addrummond/mlm/firmware/capsense.c

#include <capsense.h>
#include <config.h>
#include <const.h>
#include <em_acmp.h>
#include <em_cmu.h>
#include <em_emu.h>
#include <em_gpio.h>
#include <em_lesense.h>
#include <em_wdog.h>
#include <em_pcnt.h>
#include <em_prs.h>
#include <em_rtc.h>
#include <leds.h>
#include <myemu.h>
#include <rtc.h>
#include <rtt.h>
#include <stdbool.h>
#include <time.h>

// https://www.silabs.com/content/usergenerated/asi/cloud/attachments/siliconlabs/en/community/mcu/32-bit/knowledge-base/jcr:content/content/primary/blog/low_power_capa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

static uint32_t touch_chan;
static uint32_t touch_acmp;

static volatile uint32_t old_count;

uint32_t calibration_values[3] __attribute__((section (".persistent")));
uint32_t le_calibration_center_pad_value __attribute__((section (".persistent")));
uint32_t le_calibration_center_pad_threshold __attribute__((section (".persistent")));

static const uint32_t THRESHOLD_FRAC = 218;
// The left and right buttons are often pressed with the edge of the thumb, so a little more sensitivity is needed.
static const uint32_t LEFT_RIGHT_THRESHOLD_FRAC = 223;

static const PCNT_Init_TypeDef initPCNT =
{
    .mode        = pcntModeExtSingle, // External, single mode.
    .counter     = 0,                 // Counter value has been initialized to 0.
    .top         = 0xFFFF,            // Counter top value.
    .negEdge     = false,             // Use positive edge.
    .countDown   = false,             // Up-counting.
    .filter      = false,             // Filter disabled.
    .hyst        = false,             // Hysteresis disabled.
    .s1CntDir    = false,             // Counter direction is given by S1.
    .cntEvent    = pcntCntEventUp,    // Regular counter counts up on upcount events.
    .auxCntEvent = pcntCntEventNone,  // Auxiliary counter doesn't respond to events.
    .s0PRS       = pcntPRSCh0,        // PRS channel 0 selected as S0IN.
    .s1PRS       = pcntPRSCh1         // PRS channel 1 selected as S1IN.
};

void setup_capsense()
{
    ACMP_CapsenseInit_TypeDef capsenseInit = ACMP_CAPSENSE_INIT_DEFAULT;
    CMU_ClockEnable(cmuClock_ACMP0, true);
    CMU_ClockEnable(cmuClock_ACMP1, true);
    CMU_ClockEnable(cmuClock_PRS, true);
    CMU_ClockEnable(cmuClock_PCNT0, true);
    ACMP_CapsenseInit(ACMP0, &capsenseInit);
    ACMP_CapsenseInit(ACMP1, &capsenseInit);

    while (!(ACMP0->STATUS & ACMP_STATUS_ACMPACT) || !(ACMP1->STATUS & ACMP_STATUS_ACMPACT))
        ;

    PRS_SourceAsyncSignalSet(0, PRS_CH_CTRL_SOURCESEL_ACMP0, PRS_CH_CTRL_SIGSEL_ACMP0OUT);

    PCNT_Init(PCNT0, &initPCNT);

    PCNT_PRSInputEnable(PCNT0, pcntPRSInputS0, true);

    // Sync up to end PCNT initialization
    while (PCNT0->SYNCBUSY)
    {
        PRS_LevelSet(PRS_SWLEVEL_CH0LEVEL, PRS_SWLEVEL_CH0LEVEL);
        PRS_LevelSet(~PRS_SWLEVEL_CH0LEVEL, PRS_SWLEVEL_CH0LEVEL);
    }

    ACMP_CapsenseChannelSet(ACMP0, acmpChannel1);

    touch_acmp = 0;
    touch_chan = 0;
    old_count = 0;
}

void disable_capsense()
{
    PCNT_PRSInputEnable(PCNT0, pcntPRSInputS0, false);
    PCNT_Enable(PCNT0, pcntModeDisable);
    ACMP0->CTRL &= ~ACMP_CTRL_IRISE_ENABLED;
    ACMP1->CTRL &= ~ACMP_CTRL_IRISE_ENABLED;
    ACMP_Disable(ACMP0);
    ACMP_Disable(ACMP1);
    NVIC_ClearPendingIRQ(ACMP0_IRQn);
    NVIC_DisableIRQ(ACMP0_IRQn);
    CMU_ClockEnable(cmuClock_ACMP0, false);
    CMU_ClockEnable(cmuClock_ACMP1, false);
    CMU_ClockEnable(cmuClock_PRS, false);
    CMU_ClockEnable(cmuClock_PCNT0, false);
}

void cycle_capsense()
{
    PCNT_PRSInputEnable(PCNT0, pcntPRSInputS0, false);

    if (touch_acmp == 0) {
        if (touch_chan == 0) {
            ACMP_CapsenseChannelSet(ACMP0, acmpChannel1);
            touch_chan = 1;
        } else {
            ACMP0->CTRL &= ~ACMP_CTRL_IRISE_ENABLED;
            ACMP1->CTRL |= ACMP_CTRL_IRISE_ENABLED;
            ACMP_CapsenseChannelSet(ACMP1, acmpChannel6);
            PRS_SourceAsyncSignalSet(0, PRS_CH_CTRL_SOURCESEL_ACMP1, PRS_CH_CTRL_SIGSEL_ACMP1OUT);
            touch_acmp = 1;
            touch_chan = 0;
        }
    } else {
        ACMP1->CTRL &= ~ACMP_CTRL_IRISE_ENABLED;
        ACMP0->CTRL |= ACMP_CTRL_IRISE_ENABLED;
        ACMP_CapsenseChannelSet(ACMP0, acmpChannel0);
        PRS_SourceAsyncSignalSet(0, PRS_CH_CTRL_SOURCESEL_ACMP0, PRS_CH_CTRL_SIGSEL_ACMP0OUT);

        touch_acmp = 0;
        touch_chan = 0;
    }

    PCNT_PRSInputEnable(PCNT0, pcntPRSInputS0, true);

    // Sync up to end PCNT initialization
    while (PCNT0->SYNCBUSY)
    {
        PRS_LevelSet(PRS_SWLEVEL_CH0LEVEL, PRS_SWLEVEL_CH0LEVEL);
        PRS_LevelSet(~PRS_SWLEVEL_CH0LEVEL, PRS_SWLEVEL_CH0LEVEL);
    }

    old_count = PCNT0->CNT;
}

void calibrate_capsense()
{
    setup_capsense();

    delay_ms_cyc_prepare {
        get_touch_count(0, 0, 0); // clear any nonsense values
    }
    uint32_t ellapsed = delay_ms_cyc(PAD_COUNT_MS);

    uint32_t count, chan;
    uint32_t chans_done = 0;
    do {
        get_touch_count(&count, &chan, ellapsed);
        if (! (chans_done & (1 << chan))) {
            calibration_values[chan] = count;
            chans_done |= (1 << chan);
        }
        
        cycle_capsense();
        delay_ms_cyc_prepare {
            get_touch_count(0, 0, 0); // clear any nonsense value
        }

        ellapsed = delay_ms_cyc(PAD_COUNT_MS);
    } while (chans_done != 0b111);

    disable_capsense();

    SEGGER_RTT_printf(0, "Touch calibration: %u %u %u\n", calibration_values[0], calibration_values[1], calibration_values[2]);
}

void calibrate_le_capsense()
{
    setup_le_capsense_oneshot();
    my_emu_enter_em2(true);
    le_calibration_center_pad_value = lesense_result;
    le_calibration_center_pad_threshold = le_calibration_center_pad_value * THRESHOLD_FRAC / 256;
    disable_le_capsense();

    SEGGER_RTT_printf(0, "LE touch calibration: %u\n", le_calibration_center_pad_value);
}

static uint32_t rat0nopress, rat1nopress, rat2nopress, rat3nopress, rat4nopress;

touch_position get_touch_position(uint32_t chan0, uint32_t chan1, uint32_t chan2)
{
    // Generous margin here because temperature changes can have quite a large effect.
    if (chan0 > calibration_values[0] * 3 || chan1 > calibration_values[1] * 3 || chan2 > calibration_values[2] * 3)
        return NO_TOUCH_DETECTED;

    if (rat0nopress == 0) {
        rat0nopress = (calibration_values[0] << 8) / calibration_values[2];
        rat1nopress = (calibration_values[1] << 8) / calibration_values[2];
        rat2nopress = (calibration_values[2] << 8) / (calibration_values[0] + calibration_values[1]);

        rat3nopress = (calibration_values[0] << 8) / calibration_values[1];
        rat4nopress = (calibration_values[1] << 8) / calibration_values[0];
    }

    uint32_t rat0 = (chan0 << 8) / chan2;
    uint32_t rat1 = (chan1 << 8) / chan2;
    uint32_t rat2 = (chan2 << 8) / (chan0 + chan1);
    uint32_t rat3 = (chan0 << 8) / chan1;
    uint32_t rat4 = (chan1 << 8) / chan0;

    if (rat0 < THRESHOLD_FRAC * rat0nopress / 256 && rat1 < rat1nopress * THRESHOLD_FRAC / 256)
        return LEFT_AND_RIGHT_BUTTONS;
    if (rat2 < THRESHOLD_FRAC * rat2nopress / 256)
        return CENTER_BUTTON;
    if (rat0 < LEFT_RIGHT_THRESHOLD_FRAC * rat0nopress / 256 && rat3 < THRESHOLD_FRAC * rat3nopress / 256)
        return RIGHT_BUTTON;
    if (rat1 < LEFT_RIGHT_THRESHOLD_FRAC * rat1nopress / 256 && rat4 < THRESHOLD_FRAC * rat4nopress / 256)
        return LEFT_BUTTON;

    return NO_TOUCH_DETECTED;
}

bool le_center_pad_is_touched(uint32_t chan2)
{
    return chan2 != 0 && chan2 < le_calibration_center_pad_threshold;
}

uint32_t get_touch_count_func(uint32_t *chan_value, uint32_t *chan, uint32_t millisecond_sixteenths, const char *src_pos)
{
    if (chan != 0)
        *chan = (touch_acmp << 1) | touch_chan;

    uint32_t raw_count = PCNT0->CNT;

    if (millisecond_sixteenths > PAD_COUNT_MS*16*2) {
        if (chan_value != 0)
            *chan_value = ((1 << 30)-1) | (1 << 30);
        old_count = PCNT0->CNT;
        return raw_count;
    }

    uint32_t uncompensated_count;
    if (chan_value != 0) {
        if (raw_count >= old_count)
            uncompensated_count = raw_count - old_count;
        else
            uncompensated_count = ((1 << PCNT0_CNT_SIZE) + raw_count) - old_count;

        // Note that millisecond_sixteenths should always be >= (PAD_COUNT_MS * 16)
        uint32_t compensated_count = (uncompensated_count * (PAD_COUNT_MS * 16)) / millisecond_sixteenths;
        *chan_value = compensated_count;
    }

    old_count = PCNT0->CNT;

    return raw_count;
}

static const uint16_t LESENSE_ACMP_VDD_SCALE = 0x37U;

#define LESENSE_CAPSENSE_CH_CONF_SLEEP                                                                   \
  {                                                                                                      \
    true,                     /* Enable scan channel. */                                                 \
    true,                     /* Enable the assigned pin on scan channel. */                             \
    true,                     /* Enable interrupts on channel. */                                        \
    lesenseChPinExDis,        /* GPIO pin is disabled during the excitation period. */                   \
    lesenseChPinIdleDis,      /* GPIO pin is disabled during the idle period. */                         \
    false,                    /* Don't use alternate excitation pins for excitation. */                  \
    false,                    /* Disabled to shift results from this channel to the decoder register. */ \
    false,                    /* Disabled to invert the scan result bit. */                              \
    true,                     /* Enabled to store counter value in the result buffer. */                 \
    lesenseClkLF,             /* Use the LF clock for excitation timing. */                              \
    lesenseClkLF,             /* Use the LF clock for sample timing. */                                  \
    0,                        /* Excitation time is set to 0 excitation clock cycles. */                 \
    LE_PAD_CLOCK_COUNT,       /* Sample delay */                                                         \
    0,                        /* Measure delay */                                                        \
    LESENSE_ACMP_VDD_SCALE,   /* ACMP threshold has been set to LESENSE_ACMP_VDD_SCALE. */               \
    lesenseSampleModeCounter, /* Counter will be used in comparison. */                                  \
    lesenseSetIntLevel,       /* Interrupt is generated if the sensor triggers. */                       \
    0x00,                     /* Counter threshold has been set to 0x0. */                               \
    lesenseCompModeLess       /* Compare mode has been set to trigger interrupt on >= */                 \
  }

#define LESENSE_CAPSENSE_CH_CONF_SENSE                                                                   \
  {                                                                                                      \
    true,                     /* Enable scan channel. */                                                 \
    true,                     /* Enable the assigned pin on scan channel. */                             \
    false,                    /* Disable interrupts on channel. */                                       \
    lesenseChPinExDis,        /* GPIO pin is disabled during the excitation period. */                   \
    lesenseChPinIdleDis,      /* GPIO pin is disabled during the idle period. */                         \
    false,                    /* Don't use alternate excitation pins for excitation. */                  \
    false,                    /* Disabled to shift results from this channel to the decoder register. */ \
    false,                    /* Disabled to invert the scan result bit. */                              \
    true,                     /* Enabled to store counter value in the result buffer. */                 \
    lesenseClkLF,             /* Use the LF clock for excitation timing. */                              \
    lesenseClkLF,             /* Use the LF clock for sample timing. */                                  \
    0,                        /* Excitation time is set to ___ excitation clock cycles. */               \
    LE_PAD_CLOCK_COUNT,       /* Sample delay is set to ___ sample clock cycles. */                      \
    0,                        /* Measure delay is set to ___ excitation clock cycles.*/                  \
    LESENSE_ACMP_VDD_SCALE,   /* ACMP threshold has been set to LESENSE_ACMP_VDD_SCALE. */               \
    lesenseSampleModeCounter, /* ACMP will be used in comparison. */                                     \
    lesenseSetIntLevel,       /* Interrupt is generated if the sensor triggers. */                       \
    0x0,                      /* Counter threshold has been set to 0x00. */                              \
    lesenseCompModeLess       /* Compare mode has been set to trigger interrupt on "less". */            \
  }

static CONST_IN_RAM LESENSE_ChDesc_TypeDef chanConfigSense = LESENSE_CAPSENSE_CH_CONF_SENSE;
static CONST_IN_RAM LESENSE_ChDesc_TypeDef chanConfigSleep = LESENSE_CAPSENSE_CH_CONF_SLEEP;

static CONST_IN_RAM LESENSE_Init_TypeDef initLESENSE =
{
    .coreCtrl = {
        .scanStart    = lesenseScanStartPeriodic,
        .prsSel       = lesensePRSCh0,
        .scanConfSel  = lesenseScanConfDirMap,
        .invACMP0     = false,
        .invACMP1     = false,
        .dualSample   = false,
        .storeScanRes = false,
        .bufOverWr    = true,
        .bufTrigLevel = lesenseBufTrigHalf,
        .wakeupOnDMA  = lesenseDMAWakeUpDisable,
        .biasMode     = lesenseBiasModeDutyCycle,
        .debugRun     = false
    },

    .timeCtrl = {
        .startDelay = 0U
    },

    .perCtrl = {
        .dacCh0Data     = lesenseDACIfData,
        .dacCh0ConvMode = lesenseDACConvModeDisable,
        .dacCh0OutMode  = lesenseDACOutModeDisable,
        .dacCh1Data     = lesenseDACIfData,
        .dacCh1ConvMode = lesenseDACConvModeDisable,
        .dacCh1OutMode  = lesenseDACOutModeDisable,
        .dacPresc       = 0U,
        .dacRef         = lesenseDACRefBandGap,
        .acmp0Mode      = lesenseACMPModeDisable,
        .acmp1Mode      = lesenseACMPModeMuxThres,
        .warmupMode     = lesenseWarmupModeNormal
    },

    .decCtrl = {
        .decInput  = lesenseDecInputSensorSt,
        .chkState  = false,
        .intMap    = true,
        .hystPRS0  = false,
        .hystPRS1  = false,
        .hystPRS2  = false,
        .hystIRQ   = false,
        .prsCount  = true,
        .prsChSel0 = lesensePRSCh0,
        .prsChSel1 = lesensePRSCh1,
        .prsChSel2 = lesensePRSCh2,
        .prsChSel3 = lesensePRSCh3
    }
};

static le_capsense_mode le_mode;

static uint32_t le_center_pad_count_to_threshold(uint32_t count)
{
    return count * THRESHOLD_FRAC / 256;
}

static void setup_le_capsense_helper(const LESENSE_ChDesc_TypeDef *chan_config, const LESENSE_ScanMode_TypeDef scan_mode, uint32_t scan_freq)
{
    CMU_ClockEnable(cmuClock_ACMP1, true);
    CMU_ClockEnable(cmuClock_LESENSE, true);

    CMU_ClockDivSet(cmuClock_LESENSE, cmuClkDiv_16);

    GPIO_DriveModeSet(gpioPortC, gpioDriveModeStandard);

    static CONST_IN_RAM ACMP_CapsenseInit_TypeDef initACMP = {
        .fullBias                 = true,
        .halfBias                 = true,
        .biasProg                 = 0x7,
        .warmTime                 = acmpWarmTime512,
        .hysteresisLevel          = acmpHysteresisLevel5,
        .resistor                 = acmpResistor0,
        .lowPowerReferenceEnabled = false,
        .vddLevel                 = 0x30,
        .enable                   = false
    };

    ACMP_GPIOSetup(ACMP1, 0, false, false);

    ACMP_CapsenseInit(ACMP1, &initACMP);

    LESENSE_Init(&initLESENSE, true);

    LESENSE_ScanStop();
    while (LESENSE_STATUS_SCANACTIVE & LESENSE_StatusGet())
        ;
    LESENSE_ResultBufferClear();
    LESENSE_ScanFreqSet(0, scan_freq);
    LESENSE_ClkDivSet(lesenseClkLF, lesenseClkDiv_1);

    LESENSE_ChannelConfig(chan_config, 14);

    NVIC_EnableIRQ(LESENSE_IRQn);

    LESENSE_ScanModeSet(scan_mode, true);
}

void setup_le_capsense_oneshot()
{
    le_mode = LE_CAPSENSE_SENSE;
    setup_le_capsense_helper(&chanConfigSense, lesenseScanStartOneShot, 0);
    LESENSE_IntEnable(LESENSE_IEN_SCANCOMPLETE);
}

void setup_le_capsense_sleep()
{
    le_mode = LE_CAPSENSE_SLEEP;

    setup_le_capsense_helper(&chanConfigSleep, lesenseScanStartPeriodic, NORMAL_PAD_SCAN_HZ);

    LESENSE_IntDisable(LESENSE_IEN_SCANCOMPLETE);

    while (!(LESENSE->STATUS & LESENSE_STATUS_BUFHALFFULL))
        ;
    LESENSE_ChannelThresSet(14, LESENSE_ACMP_VDD_SCALE, le_center_pad_count_to_threshold(le_calibration_center_pad_value));

    // Periodically wake up to recalibrate.
    SEGGER_RTT_printf(0, "Set recal. wakeup timer.\n");
    static CONST_IN_RAM RTC_Init_TypeDef rtc_init = {
        .enable   = true,
        .debugRun = false,
        .comp0Top = true
    };
    RTC_Init(&rtc_init);
    RTC_IntEnable(RTC_IEN_COMP0);
    NVIC_EnableIRQ(RTC_IRQn);
    set_rtc_clock_div(cmuClkDiv_32768);
    RTC_CompareSet(0, RTC->CNT + LE_CAPSENSE_CALIBRATION_INTERVAL_SECONDS);
    RTC_IntClear(RTC_IFC_COMP0);
}

void le_capsense_slow_scan()
{
    LESENSE_ScanFreqSet(0, SLOW_PAD_SCAN_HZ);
}

uint32_t lesense_result;

static volatile bool irq_handler_triggered;

void reset_lesense_irq_handler_state()
{
    irq_handler_triggered = false;
}

bool check_lesense_irq_handler()
{
    bool v = irq_handler_triggered;
    irq_handler_triggered = false;
    return v;
}

void LESENSE_IRQHandler(void)
{
    irq_handler_triggered = true;

    LESENSE_IntClear(LESENSE_IEN_SCANCOMPLETE);
    LESENSE_IntClear(LESENSE_IF_CH14);

    lesense_result = LESENSE_ScanResultDataGet();

    // Stop additional interrupts screwing things up by setting threshold to zero.
    if (le_mode == LE_CAPSENSE_SLEEP)
        LESENSE_ChannelThresSet(14, LESENSE_ACMP_VDD_SCALE, 0);
}

static uint32_t get_max_value(volatile uint32_t* A, int N){
    int i;
    uint32_t max = 0;

    for (i = 0; i < N; i++) {
        if (max < A[i])
            max = A[i];
    }

    return max;
}

#define NUMBER_OF_LE_CALIBRATION_VALUES 5
#define NUM_LESENSE_CHANNELS            1

// Adapted from example code in AN0028.
void recalibrate_le_capsense()
{
    SEGGER_RTT_printf(0, "Recal. capsense.\n");

    static uint32_t channels_used_mask;
    static const int num_channels_used = 1;
    static volatile uint32_t calibration_value[NUM_LESENSE_CHANNELS][NUMBER_OF_LE_CALIBRATION_VALUES];
    static volatile uint32_t channel_max_value[NUM_LESENSE_CHANNELS];

    int i, k;
    static uint8_t calibration_value_index = 0;

    // Wait for current scan to finish
    while (LESENSE->STATUS & LESENSE_STATUS_SCANACTIVE)
        ;

    // Get position for first channel data in count buffer from lesense write pointer
    k = ((LESENSE->PTR & _LESENSE_PTR_WR_MASK) >> _LESENSE_PTR_WR_SHIFT);

    // Handle circular buffer wraparound
    if (k >= num_channels_used)
        k = k - num_channels_used;
    else
        k = k - num_channels_used + NUM_LESENSE_CHANNELS;

    // Fill calibration values array with buffer values
    for (i = 0; i < NUM_LESENSE_CHANNELS; i++) {
        if ((channels_used_mask >> i) & 0x1)
            calibration_value[i][calibration_value_index] = LESENSE_ScanResultDataBufferGet(k++);
    }

    // Wrap around calibration_values_index
    calibration_value_index++;
    if (calibration_value_index >= NUMBER_OF_LE_CALIBRATION_VALUES)
        calibration_value_index = 0;

    // Calculate max value for each channel and set threshold
    for (i = 0; i < NUM_LESENSE_CHANNELS; i++) {
        if ((channels_used_mask >> i) & 0x1) {
            channel_max_value[i] = get_max_value(calibration_value[i], NUMBER_OF_LE_CALIBRATION_VALUES);

            le_calibration_center_pad_value = channel_max_value[i];
            le_calibration_center_pad_threshold = le_calibration_center_pad_value * THRESHOLD_FRAC / 256;
            LESENSE_ChannelThresSet(14, LESENSE_ACMP_VDD_SCALE, le_center_pad_count_to_threshold(le_calibration_center_pad_value));
        }
    }
}

void disable_le_capsense()
{
    if (le_mode == LE_CAPSENSE_SLEEP) {
        RTC_IntDisable(RTC_IEN_COMP0);
        NVIC_DisableIRQ(RTC_IRQn);
        LESENSE_ChannelThresSet(14, LESENSE_ACMP_VDD_SCALE, 0);
    }

    LESENSE_ScanStop();

    while (LESENSE_STATUS_SCANACTIVE & LESENSE_StatusGet())
        ;

    ACMP_Disable(ACMP1);

    CMU_ClockEnable(cmuClock_ACMP1, false);
    CMU_ClockEnable(cmuClock_LESENSE, false);

    CMU_ClockDivSet(cmuClock_LESENSE, cmuClkDiv_1);

    LESENSE_Reset();

    NVIC_DisableIRQ(LESENSE_IRQn);
}

static const int MAX_MISS_COUNT = 2;

press get_pad_press_func(touch_position touch_pos, uint32_t nloops)
{
    press p;

    int miss_count = 0;
    uint32_t chans[] = { 0, 0, 0 };
    uint32_t ellapsed;
    for (uint32_t i = 0;; ++i) {
        delay_ms_cyc_prepare {
            get_touch_count(0, 0, 0); // clear any nonsense value
        }
        ellapsed = delay_ms_cyc(PAD_COUNT_MS);

        uint32_t count, chan;
        get_touch_count(&count, &chan, ellapsed);
        chans[chan] = count;

        if (chans[0] != 0 && chans[1] != 0 && chans[2] != 0) {
            touch_position tp = get_touch_position(chans[0], chans[1], chans[2]);
            if (tp != touch_pos) {
                ++miss_count;
                if (miss_count > MAX_MISS_COUNT) {
                    p = PRESS_TAP;
                    break;
                }
            }
        }

        // The time it takes to execute the code in this loop is short compared
        // to PAD_COUNT_MS, so this is tolerably accurate.
        if (i >= nloops) {
            p = PRESS_HOLD;
            break;
        }

        cycle_capsense();
    }

    return p;
}

void reset_capsense_state()
{
    rat0nopress = 0;
    rat1nopress = 0;
    rat2nopress = 0;
    rat3nopress = 0;
    rat4nopress = 0;
}
